joleiv/blubo/V3/config_manager.py

import json
import sys

class ConfigManager:
    def __init__(self, config_path="config.json"):
        try:
            with open(config_path, "r") as f:
                self.config = json.load(f)
        except Exception as e:
            print(f"Error loading config: {e}")
            sys.exit(1)
    
    def get(self, key, default=None):
        return self.config.get(key, default)
